zygurt/MIDI-Wind-Controller/src/MIDI-Sax-doppler/defines.h

//This section contains pin assignment defines
//Digital Pins 0-9 are key inputs
  //A3 is breath sensor
  //A5 is Octave buttons [0.33, 1.65, 2.97]V
  //A7 is MIDI out

//If it doesn't compile, use v1.3.0 of the Adafruit SAMD Boards

//For BPS110 pressure sensor: (BPS110-AD0P15-2DG)
//Pin 1 is Vs
//Pin 4 is GND
//Pin 6 is Vout
//The pressure transfer function is
//Ppsi = (Pmax-Pmin)*((Vout-VminComp)/(VmaxComp-VminComp))+Pmin, where:
//Ppsi = Measure Pressure in PSI
//Pmax = Maximum pressure (0.15 psi)
//Pmin = minimum pressure (1 psi)
//VminComp = Minimum Voltage (Usually 0.5V)
//VmaxComp = Maximum Voltage (Usually 4.5V)
//Vout = Output Voltage


#define BREATH_PIN A3
#define OCTAVE_PIN A5
// #define MIDI_TX_PIN A7

#define breath_threshold 20 //Breath on/off threshold
#define breath_scale 0.5 //Breath scaling factor
#define breath_array_len 8

#define CC_threshold 4
#define breath_CC 2



//This section contains all of the register defines for the dadamachines doppler
// that are being used in this project
#define PORTA 0x40000000
#define PORTB 0x41000000
#define PORTC 0x42000000
#define PORTD 0x43000000

//GPIO PORT OFFSETS
#define PORT_DIR 0x00   //Set the Port Pin direction
#define PORT_OUT 0x10   //Holds the values on the pins
#define PORT_OUTCLR 0x14  //Set an output low
#define PORT_OUTSET 0x18  //Set an output high
#define PORT_OUTTGL 0x1C  //Toggle an output value
#define PORT_IN 0x20   //Holds the input value on a pin
#define PORT_CRTL 0x24  //On demand (0) or Continuous (1) input sampling
#define PORT_WRCONFIG 0x28 //Used for setting configuration of multiple pins at a time p.904 datasheet
